Somnitec/Omniphone/test/led_test.cpp

#include <Arduino.h>
#include <Wire.h>
#include <MPR121.h>
#include "../variants/teensy40-11pad/config.h" // NUM_BOARDS, BOARD_ADDRESSES

// ─────────────────────────────────────────────────────────────────────────────
// LED Test  —  isolate the "ELE9/ELE10 won't light alone, work together" fault
//
// Build:  pio run -e led_test -t upload   (then open serial @115200)
//
// LEDs are on ELE6–ELE11 = GPIO2–GPIO7 = GPIO data bits 2–7 (LED index 0–5).
// The suspect pair is LED3 = ELE9 and LED4 = ELE10.
//
// Three drive modes, selectable live over serial. Each runs the same A/B/C
// pattern so you can compare them directly:
//
//   p  PROD   — production path: setAllLEDs() with real PWM dimming (bri=10).
//               Open-drain high-side LED driver. Reproduces the field bug.
//   o  ODFULL — same open-drain LED-driver mode, but PWM forced full (0x0F).
//               Removes PWM *modulation* as a variable, keeps the driver path.
//   d  DCCMOS — CMOS push-pull output, NO PWM at all. Pure digital on/off.
//               Tests the LED + wiring electrically, bypassing the MPR121
//               LED-driver/PWM subsystem entirely.
//
// Decision tree (watch LED3-alone / LED4-alone in Phase B):
//   fails in p  but OK in o   → it's the PWM duty/modulation interaction
//   fails in o  but OK in d   → it's the open-drain LED-driver mode itself
//   fails even in d           → genuine per-channel hardware (LED/resistor/pin)
//
// Phase A — each LED 0..5 alone (control: every lamp must light by itself).
// Phase B — LED3 alone, LED4 alone, LED3+LED4 (the suspect pair).
// Phase C — all on, then all off.
// Drives all boards from config.h in parallel.
// ─────────────────────────────────────────────────────────────────────────────

// LED channels: ELE6..ELE11 → GPIO bits 2..7
static constexpr uint8_t LED_MASK = 0xFC;
static inline uint8_t ledBit(uint8_t i) { return (uint8_t)(1u << (i + 2)); }

static MPR121 boards[NUM_BOARDS] = {
    MPR121(BOARD_ADDRESSES[0]),
    MPR121(BOARD_ADDRESSES[1]),
};

enum Mode : uint8_t { MODE_PROD, MODE_ODFULL, MODE_DCCMOS };
static Mode mode = MODE_DCCMOS; // default = the no-PWM electrical test

// Which board(s) are driven: 0 = board0 only, 1 = board1 only, 2 = both.
static uint8_t boardSel = 2;
static inline bool boardActive(uint8_t b) { return boardSel == 2 || boardSel == b; }

// Stepping: manual=false auto-advances; manual=true waits for 'n' between steps.
static bool    manual   = false;
static bool    stepNext = false;
static uint8_t stepIdx  = 0;
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
